pavelpolach321/SOASENSE/Firmware/src/main.h

#ifndef MAIN_H
#define MAIN_H

#include "../node_setup/setup.h"
#include "hardware/pcf8574_expander.h"
#include "ui/ui.h"
#include <esp_task_wdt.h>
//#include "LMIC/LMIC-node.h"

#define USE_WIFI      0
#define USE_LORAWAN   1

#endif
