pavelpolach321/SOASENSE/Firmware/src/hardware/sensirion-scd4x.cpp

#include <Arduino.h>
#include <SensirionI2CScd4x.h>
#include <Wire.h>

SensirionI2CScd4x scd4x;

void printUint16Hex(uint16_t value) {
    Serial.print(value < 4096 ? "0" : "");
    Serial.print(value < 256 ? "0" : "");
    Serial.print(value < 16 ? "0" : "");
    Serial.print(value, HEX);
}

void printSerialNumber(uint16_t serial0, uint16_t serial1, uint16_t serial2) {
    Serial.print("Serial: 0x");
    printUint16Hex(serial0);
    printUint16Hex(serial1);
    printUint16Hex(serial2);
    Serial.println();
}

#include "hardware.h"




void probeSDC4X(node_object_t *handle) {
  // Begin communication channel;
    uint16_t error;
    char errorMessage[256];

    scd4x.begin(Wire);

    // stop potentially previously started measurement
    error = scd4x.stopPeriodicMeasurement();
    if (error) {
        Serial.print("Error trying to execute stopPeriodicMeasurement(): ");
        errorToString(error, errorMessage, 256);
        Serial.println(errorMessage);
    }

    uint16_t serial0;
    uint16_t serial1;
    uint16_t serial2;
    error = scd4x.getSerialNumber(serial0, serial1, serial2);
    if (error) {
        Serial.print("Error trying to execute getSerialNumber(): ");
        errorToString(error, errorMessage, 256);
        Serial.println(errorMessage);
    } else {
        handle->probes.SCD4X_present = true;
        printSerialNumber(serial0, serial1, serial2);


        // Start Measurement
        error = scd4x.startPeriodicMeasurement();
        if (error) {
            Serial.print("Error trying to execute startPeriodicMeasurement(): ");
            errorToString(error, errorMessage, 256);
            Serial.println(errorMessage);
        }
    
        Serial.println("Waiting for first measurement... (5 sec)"); 
        return;
    }

    handle->probes.SCD4X_present = false;
}

int sdc4xUpdate(node_object_t *handle) {

       uint16_t error;
    char errorMessage[256];

    delay(100);

    // Read Measurement
    uint16_t co2 = 0;
    float temperature = 0.0f;
    float humidity = 0.0f;
    bool isDataReady = false;
    error = scd4x.getDataReadyFlag(isDataReady);
    if (error) {
        Serial.print("Error trying to execute getDataReadyFlag(): ");
        errorToString(error, errorMessage, 256);
        Serial.println(errorMessage);
        return 1;
    }
    if (!isDataReady) {
        Serial.print("Data not ready.");
        return 2;
    }
    error = scd4x.readMeasurement(co2, temperature, humidity);
    if (error) {
        Serial.print("Error trying to execute readMeasurement(): ");
        errorToString(error, errorMessage, 256);
        Serial.println(errorMessage);
    } else if (co2 == 0) {
        Serial.println("Invalid sample detected, skipping.");
    } else {
        Serial.print("Co2:");
        Serial.print(co2);
        Serial.print("\t");
        Serial.print("Temperature:");
        Serial.print(temperature);
        Serial.print("\t");
        Serial.print("Humidity:");
        Serial.println(humidity);

        handle->data.scd4x_co2 = co2;
        handle->data.scd4x_temp = (uint16_t)(temperature * 100);
        handle->data.scd4x_hum = (uint16_t)(humidity * 100);
    }

    return 0;
}
